tompi/rollino/case/renders/section_mcu.png

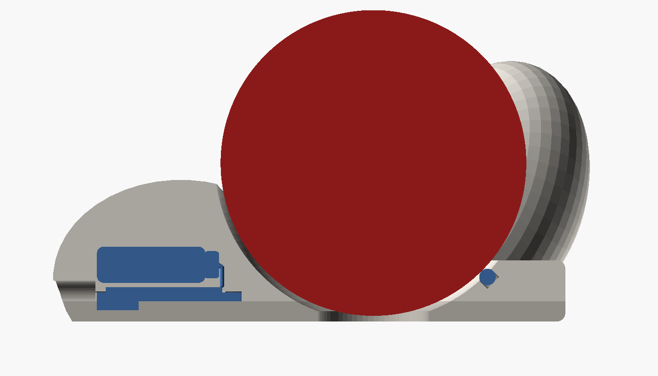
case/renders/section_mcu.png
