tompi/rollino/case/renders/section_sensor.png

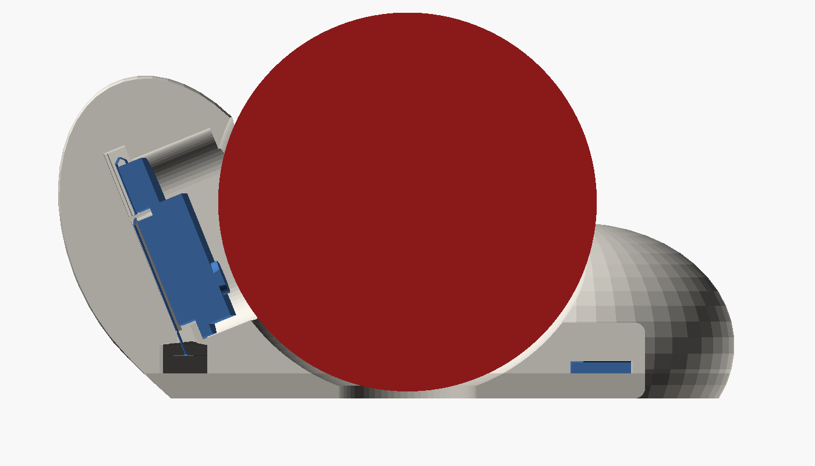
case/renders/section_sensor.png
