tompi/rollino/datasheets/RP2040-Zero-SIZE.jpg

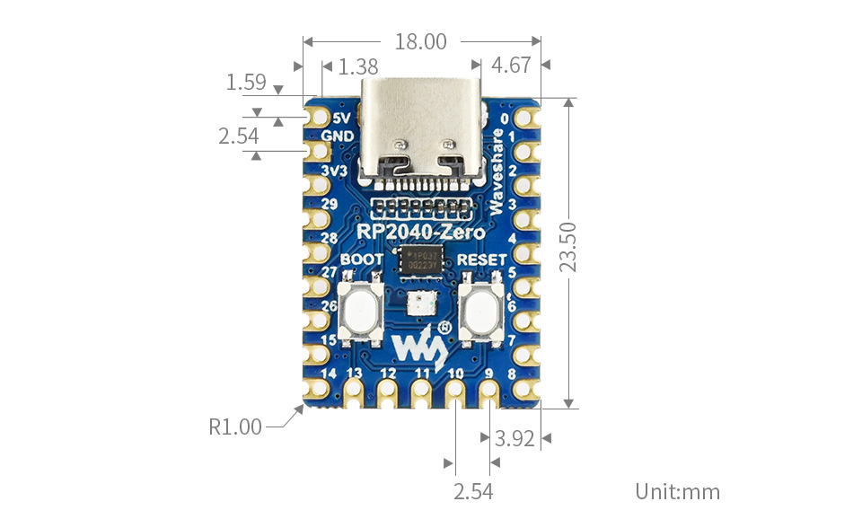
datasheets/RP2040-Zero-SIZE.jpg
