tompi/rollino/pcb/renders/base-bottom.png

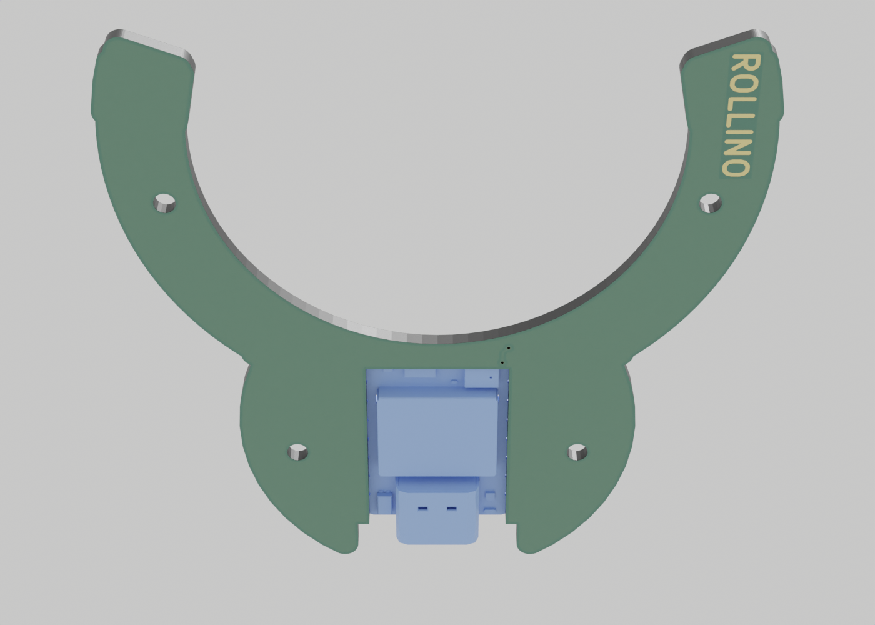
pcb/renders/base-bottom.png
