tompi/rollino/pcb/renders/base-top.png

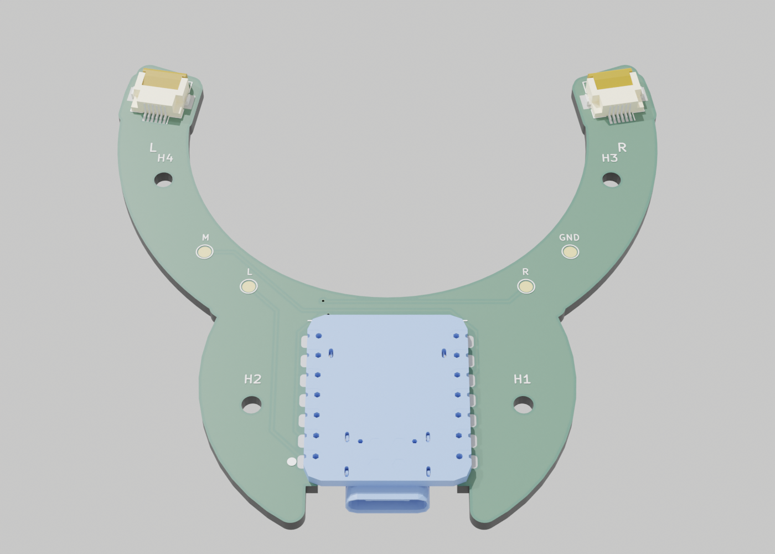
pcb/renders/base-top.png
