tompi/rollino/case/renders/assembly.png

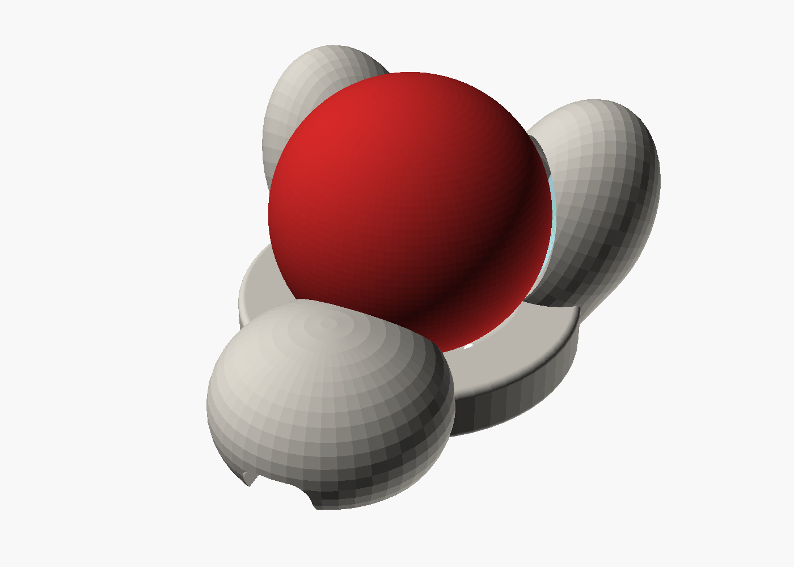
case/renders/assembly.png
